FOSH-following-demand/Open-source-Centrifuge-for-WetLab/src/Polyfuge STL Files (For 3D-Printing)/Pieces/IR Blocker.stl

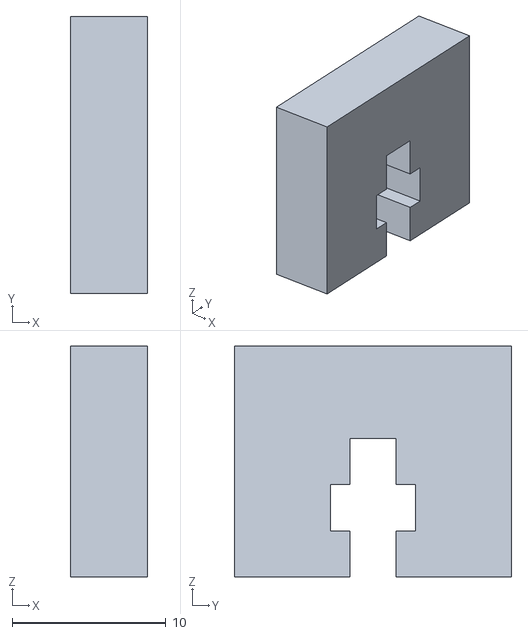
[picture p16: CAD file, 2019-08-02]
src/Polyfuge STL Files (For 3D-Printing)/Pieces/IR Blocker.stl
5.00 x 18.0 x 15.0
