FOSH-following-demand/Open-source-Centrifuge-for-WetLab/src/Polyfuge STL Files (For 3D-Printing)/Pieces/Base.stl

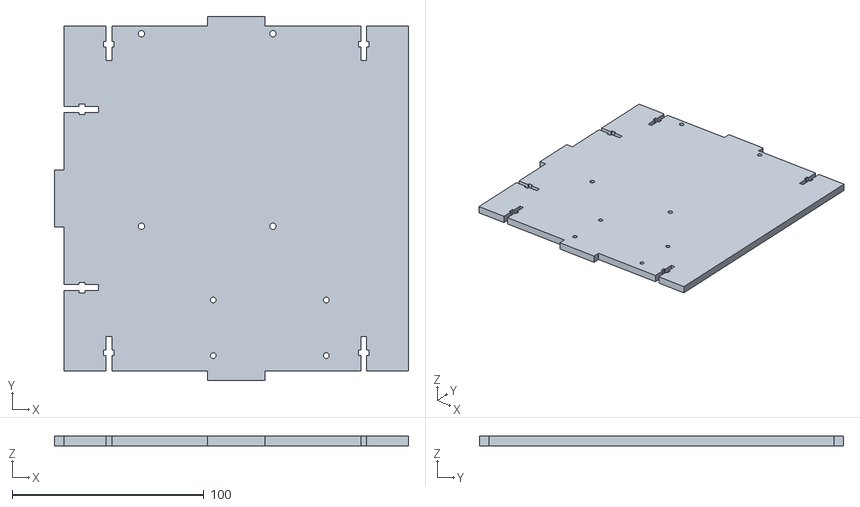
[picture p17: CAD file, 2019-08-02]
src/Polyfuge STL Files (For 3D-Printing)/Pieces/Base.stl
185.0 x 190.0 x 5.00
