FOSH-following-demand/Open-source-Centrifuge-for-WetLab/src/Polyfuge STL Files (For 3D-Printing)/Pieces/Top Panel.stl

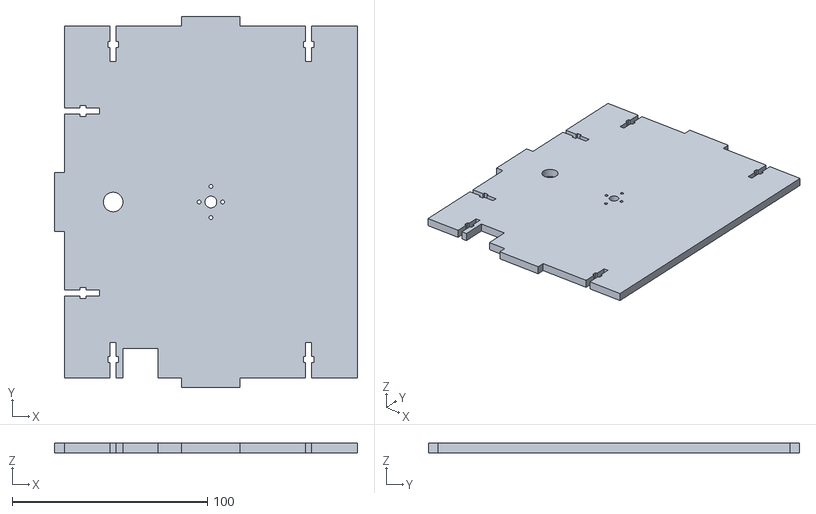
[picture p18: CAD file, 2019-08-02]
src/Polyfuge STL Files (For 3D-Printing)/Pieces/Top Panel.stl
155.0 x 190.0 x 5.00
