FOSH-following-demand/Open-source-Centrifuge-for-WetLab/src/Polyfuge STL Files (For 3D-Printing)/Pieces/Rotor.stl

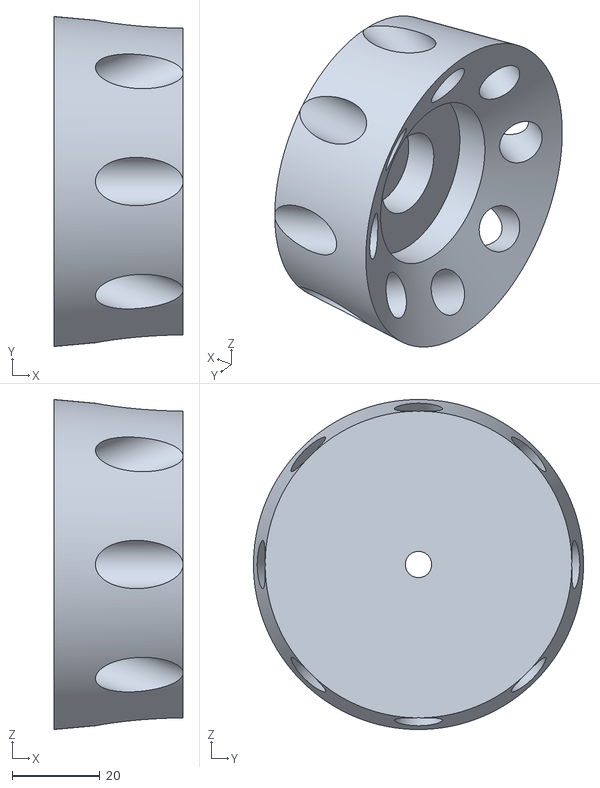
[picture p19: CAD file, 2019-08-02]
src/Polyfuge STL Files (For 3D-Printing)/Pieces/Rotor.stl
29.4 x 75.3 x 75.3
