FOSH-following-demand/Open-source-Centrifuge-for-WetLab/src/Polyfuge STL Files (For 3D-Printing)/Pieces/Side Panel (Optical).stl

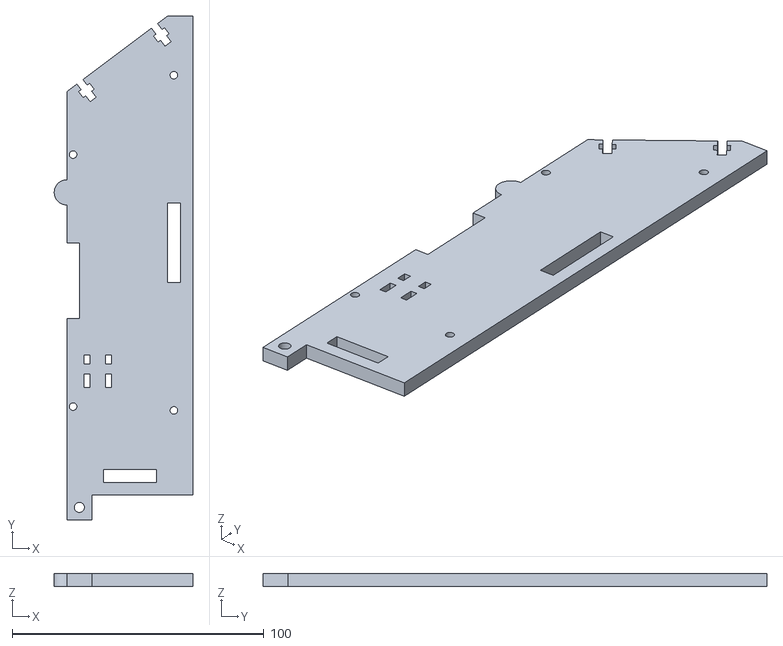
[picture p20: CAD file, 2019-08-02]
src/Polyfuge STL Files (For 3D-Printing)/Pieces/Side Panel (Optical).stl
55.0 x 200.0 x 5.00
