FOSH-following-demand/Open-source-Centrifuge-for-WetLab/src/Polyfuge STL Files (For 3D-Printing)/Pieces/knob.stl

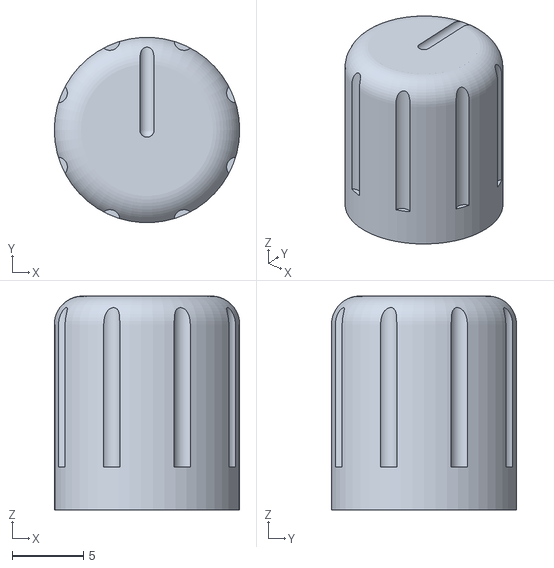
[picture p21: CAD file, 2019-08-02]
src/Polyfuge STL Files (For 3D-Printing)/Pieces/knob.stl
13.0 x 13.0 x 15.0
