FOSH-following-demand/Open-source-Centrifuge-for-WetLab/src/Polyfuge STL Files (For 3D-Printing)/Pieces/Front Panel.stl

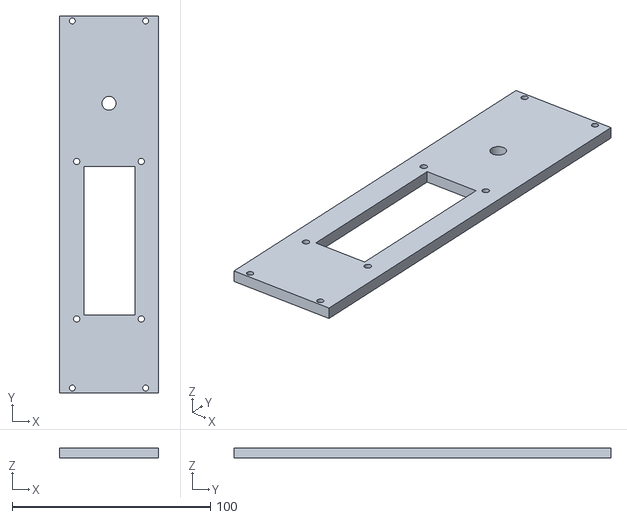
[picture p23: CAD file, 2019-08-02]
src/Polyfuge STL Files (For 3D-Printing)/Pieces/Front Panel.stl
50.0 x 190.0 x 5.00
